Dltd/OnlyFeathers/pic/OF-playlist.jpg

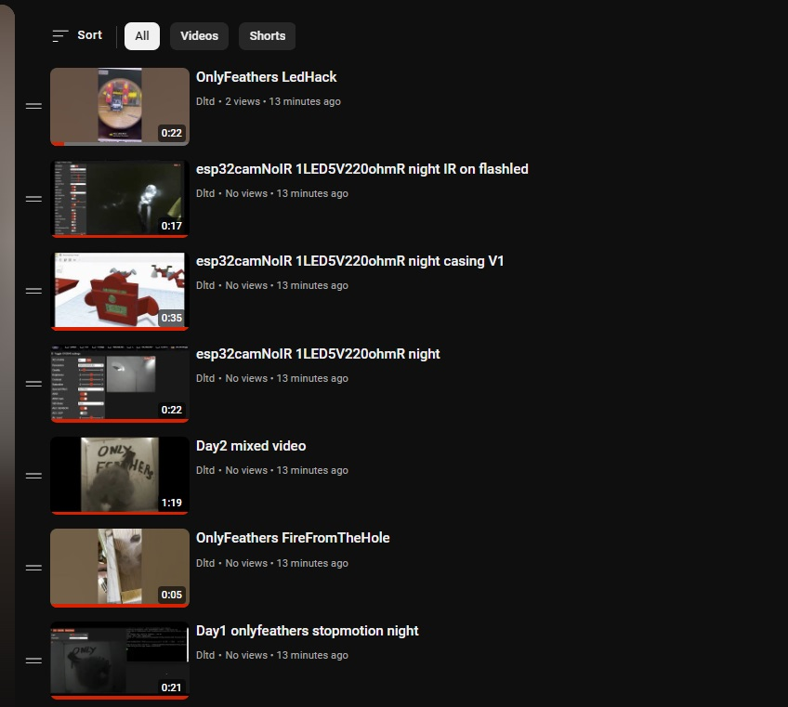
pic/OF-playlist.jpg
