Dltd/OnlyFeathers/pic/OnlyFeathers LEDhack Final LED in diffuser.png

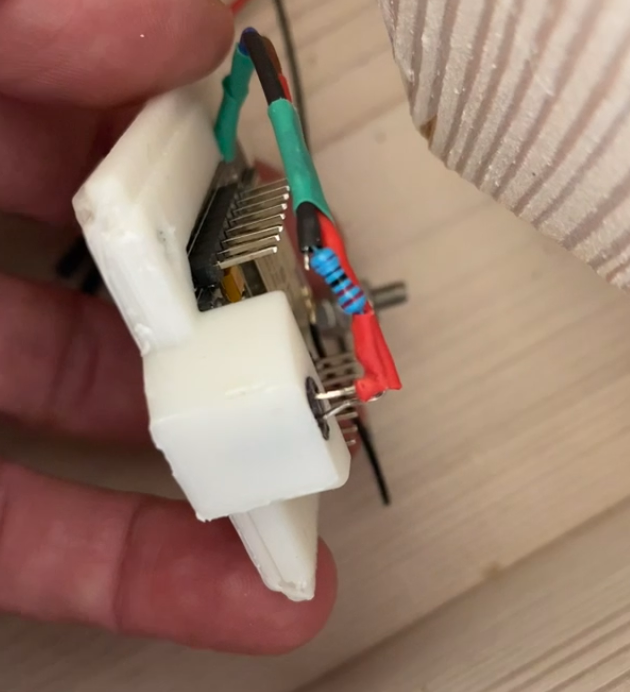
pic/OnlyFeathers LEDhack Final LED in diffuser.png
