Dltd/OnlyFeathers/pic/OnlyFeathers LEDhack Final with weight.png

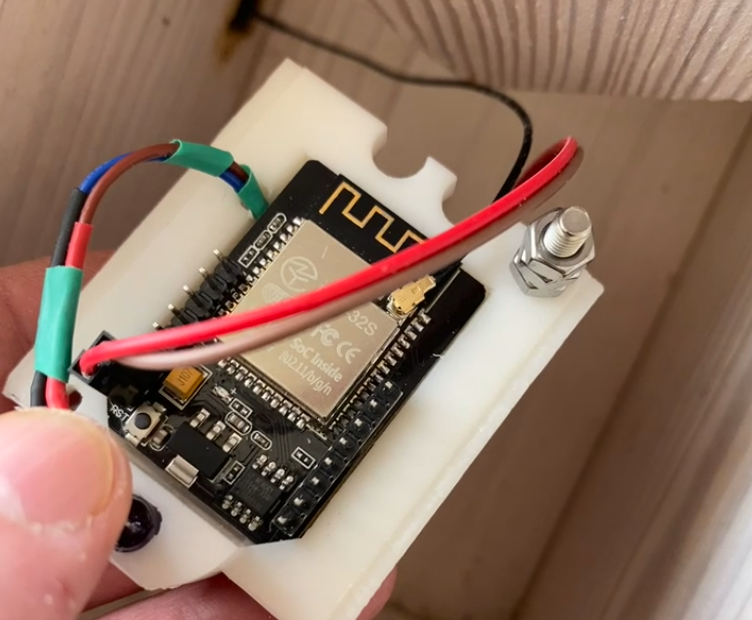
pic/OnlyFeathers LEDhack Final with weight.png
